adam-puleo/Ferrofluid-Speaker/Circuits/Main Circuit/ul_STUSB4500QTR/QFN24EP_4X4_STM-M.dxf

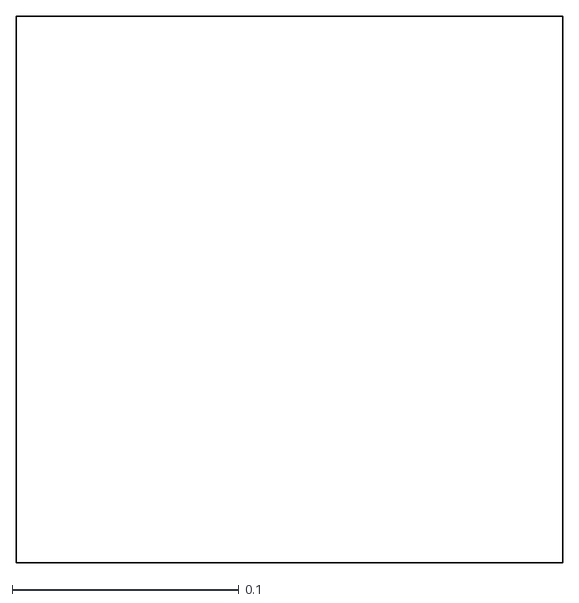
[picture p15: CAD file, 2023-05-24]
Circuits/Main Circuit/ul_STUSB4500QTR/QFN24EP_4X4_STM-M.dxf
0.241 x 0.241
