adam-puleo/Ferrofluid-Speaker/Code/ESP32/Ferrofluid-Speaker/components/TAS5805M/include/TAS5805M.hpp

#pragma once

#include "i2c-wrapper.hpp"

/** 
 * @brief Class for managing the TAS5805M amplifier.
 * @author Adam Puleo
 * @copyright Apache License Version 2
*/
class TAS5805M {
    public:
        // Constructor
        TAS5805M(i2c_wrapper *i2c_interface,
                 const gpio_num_t pdn_pin,
                 const gpio_num_t fault_pin);

        esp_err_t start_pre_i2s();
        esp_err_t start_post_i2s();
        esp_err_t stop();
        bool error();

        // Destructor
        ~TAS5805M();

    private:
        i2c_wrapper *i2c_interface;

        // Configuration parameters for the amp.
        gpio_num_t PDN;
        gpio_num_t FAULT;

        enum state_t {
            POWER_OFF,
            DEEP_SLEEP,
            HiZ,
            ON
        };
        state_t state = POWER_OFF;

        // Constants (registers) for I2C data streams.
        const uint8_t PAGE_REG = 0x00;  // Page register, see section 7.5.2.5
        const uint8_t DEVICE_CTRL_2 = 0x03;  // Section 7.6.1.3
        const uint8_t SIG_CH_CTRL = 0x28;  // Section 7.6.1.5
        const uint8_t SAP_CTRL1 = 0x33;  // Section 7.6.1.9
        const uint8_t FS_MON = 0x37;  // Section 7.6.1.12
        const uint8_t CLKDET_STATUS = 0x39;  // Section 7.6.1.14
        const uint8_t DIG_VOL_CTL = 0x4C;  // Digital volume, section 7.6.1.15
        const uint8_t AGAIN_REG = 0x54;  // Analog gain register, see section 7.3.8.1
        const uint8_t ADR_PIN_CTRL = 0x60;  // Section 7.6.1.24 
        const uint8_t ADR_PIN_CONFIG = 0x61;  // Section 7.6.1.25
        const uint8_t DIE_ID = 0x67;  // Section 7.6.1.27
        const uint8_t POWER_STATE = 0x68;  // Section 7.6.1.28
        const uint8_t CHAN_FAULT = 0x70; // Section 7.6.1.36
        const uint8_t GLOBAL_FAULT1 = 0x71; // Section 7.6.1.37
        const uint8_t GLOBAL_FAULT2 = 0x72; // Section 7.6.1.38
        const uint8_t OT_WARNING = 0x73; // Section 7.6.1.39
        const uint8_t BOOK_REG = 0x7F;  // Book register, see section 7.5.2.5
};
